darimari21/TSC/Images/1e9ec7b3-207f-4322-8b75-6b7e8333d899.PNG

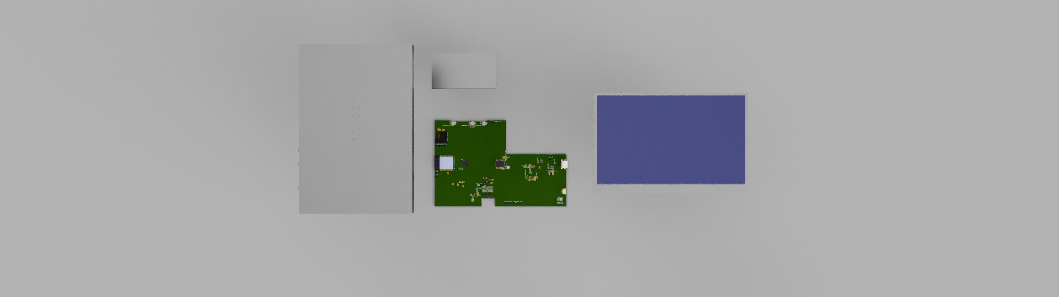
Images/1e9ec7b3-207f-4322-8b75-6b7e8333d899.PNG
