darimari21/TSC/Images/49df851a-5cd4-4d1c-8fd6-60a74a4e59ec.PNG

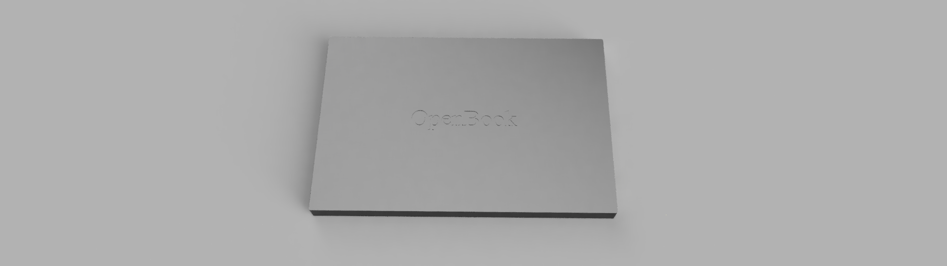
Images/49df851a-5cd4-4d1c-8fd6-60a74a4e59ec.PNG
