darimari21/TSC/Images/Screenshot 2025-04-14 140824.png

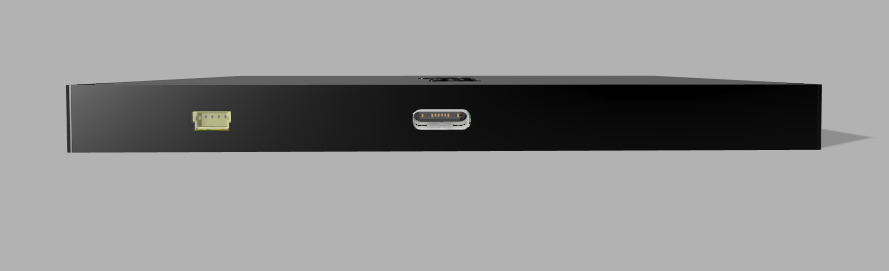
Images/Screenshot 2025-04-14 140824.png
