darimari21/TSC/Images/Screenshot 2025-04-14 141009.png

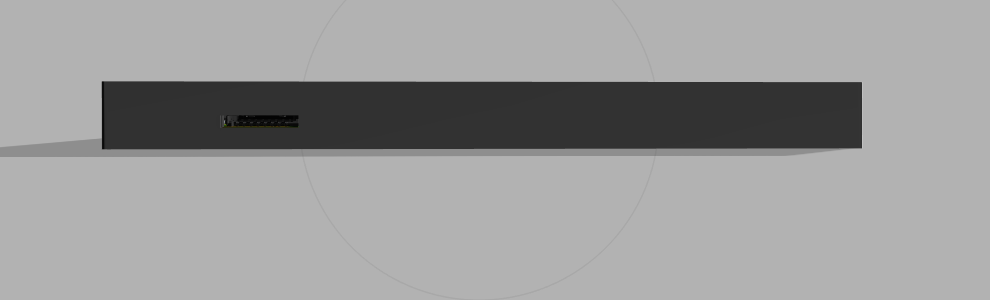
Images/Screenshot 2025-04-14 141009.png
