darimari21/TSC/Images/Screenshot 2025-04-14 141456.png

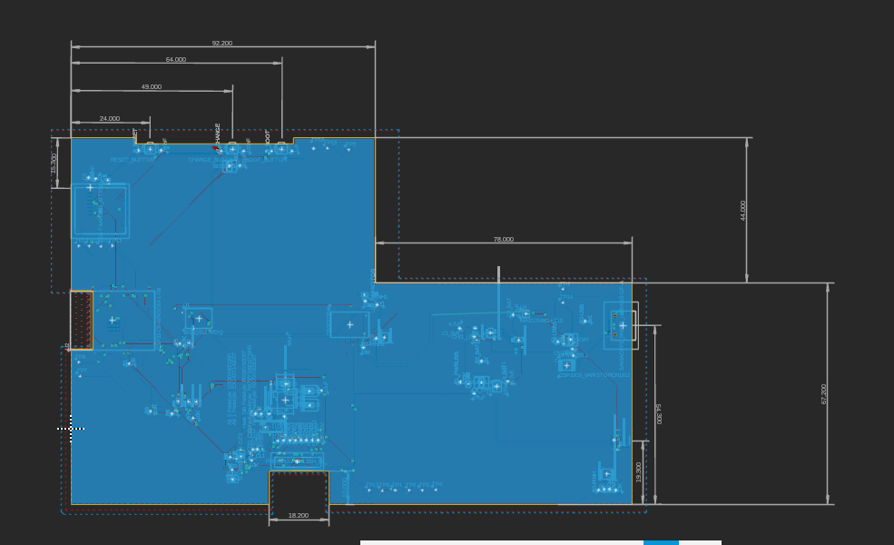
Images/Screenshot 2025-04-14 141456.png
