darimari21/TSC/Hardware/Schematic_v51.sch

## EAGLE design Hardware/Schematic_v51.sch (2025-04-06, last stored version)

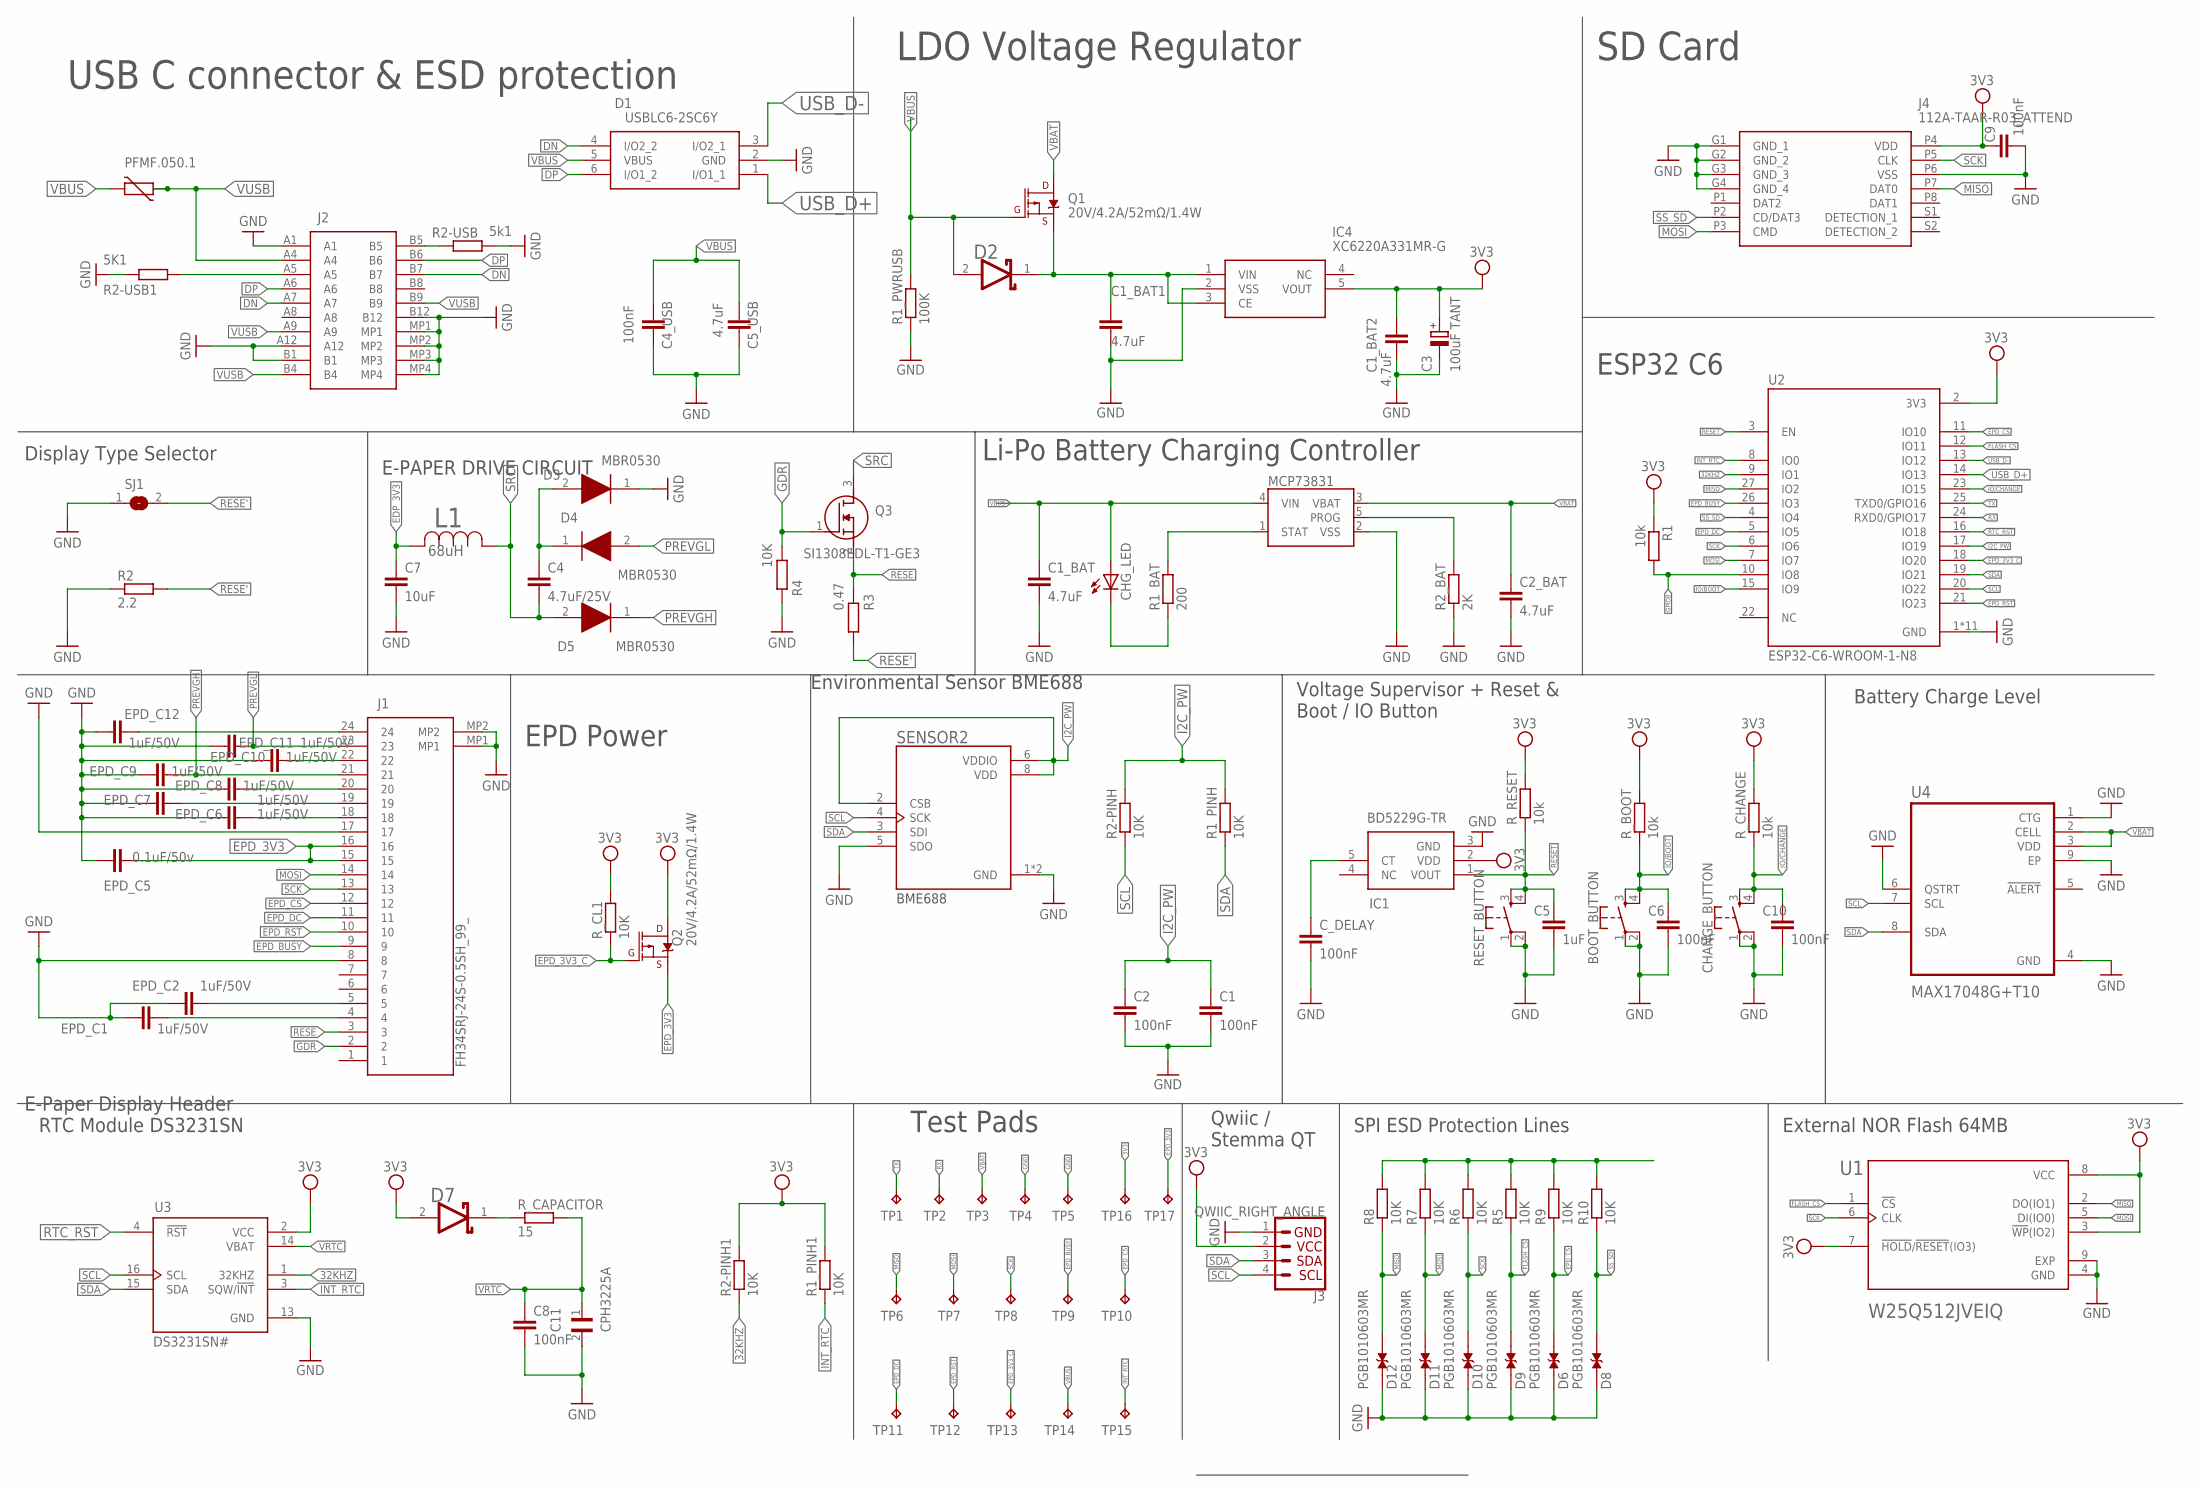
[picture p13: schematic Schematic_v51.sch]

Parts:
BOOT_BUTTON: BUTTON_CUSYOMV1; MYBUTTON
C1, C2, C4_USB, C6, C8, C9, C10: 100nF; EAGLE-LTSPICE_C0402
C1_BAT, C2_BAT, C5_USB: 4.7uF; EAGLE-LTSPICE_C0402
C1_BAT1, C1_BAT2: 4.7uF; ESP32_WROVER_EAGLE-LTSPICE_C0402
C3: 100uF TANT; RCL_CT3528
C4: 4.7uF/25V; EAGLE-LTSPICE_C0402
C5: 1uF; EAGLE-LTSPICE_C0402
C7: 10uF; EAGLE-LTSPICE_C0402
C11: CPH3225A; CAPCP3225X100N
CHANGE_BUTTON: BUTTON_CUSYOMV1; MYBUTTON
CHG_LED: ADAFRUIT_LEDCHIP-LED0603; ADAFRUIT_CHIP-LED0603
C_DELAY: 100nF; EAGLE-LTSPICE_C0402
D1: USBLC6-2SC6Y; SOT95P280X145-6N
D2, D7: ESP32_WROVER_AVX---SD0805S020S1R0_AVX_SD0805S020S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; ESP32_WROVER_AVX---SD0805S020S1R0_AVX_SD0805S020S1R0_0
D3, D4, D5: MBR0530; SOD3716X135N
D6, D8, D9, D10, D11, D12: PGB1010603MR; DIOC1608X36N
EPD_C1, EPD_C2, EPD_C6, EPD_C7, EPD_C8, EPD_C9, EPD_C10, EPD_C11, EPD_C12: 1uF/50V; EAGLE-LTSPICE_C0402
EPD_C5: 0.1uF/50v; EAGLE-LTSPICE_C0402
IC1: BD5229G-TR; SOT95P280X125-5N
IC4: XC6220A331MR-G; SOT95P280X120-5N
J1: FH34SRJ-24S-0.5SH_99_; FH34SRJ24S05SH99
J2: SAMACSYS_PARTS_USB4110-GF-A; SAMACSYS_PARTS_USB4110GFA
J3: QWIIC_RIGHT_ANGLE; JST04_1MM_RA
J4: 112A-TAAR-R03_ATTEND; 112ATAARR03ATTEND
L1: 68uH; IND_4828-WE-TPC_WRE
MCP73831: ESP32_WROVER_SPARKFUN-IC-POWER_MCP73831; ESP32_WROVER_SPARKFUN-IC-POWER_SOT23-5
PFMF.050.1: ESP32C6_VARISTORCN1812; ESP32C6_VARISTOR_CT/CN1812
Q1, Q2: 20V/4.2A/52mΩ/1.4W; ESP32_WROVER_SPARKFUN-DISCRETESEMI_SOT23-3
Q3: SI1308EDL-T1-GE3; SOT65P210X110-3N
R1: 10k; ESP32_WROVER_EAGLE-LTSPICE_R0402
R1_BAT: 200; ESP32_WROVER_EAGLE-LTSPICE_R0402
R1_PINH, R1_PINH1, R2-PINH, R2-PINH1, R4, R5, R6, R7, R8, R9, R10: 10K; ESP32_WROVER_EAGLE-LTSPICE_R0402
R1_PWRUSB: 100K; ESP32_WROVER_EAGLE-LTSPICE_R0402
R2: 2.2; ESP32_WROVER_EAGLE-LTSPICE_R0402
R2-USB: 5k1; ESP32_WROVER_EAGLE-LTSPICE_R0402
R2-USB1: 5K1; ESP32_WROVER_EAGLE-LTSPICE_R0402
R2_BAT: 2K; ESP32_WROVER_EAGLE-LTSPICE_R0402
R3: 0.47; ESP32_WROVER_EAGLE-LTSPICE_R0402
RESET_BUTTON: BUTTON_CUSYOMV1; MYBUTTON
R_BOOT: 10k; ESP32_WROVER_EAGLE-LTSPICE_R0402
R_CAPACITOR: 15; ESP32_WROVER_EAGLE-LTSPICE_R0402
R_CHANGE: 10k; ESP32_WROVER_EAGLE-LTSPICE_R0402
R_CL1: 10K; ESP32_WROVER_EAGLE-LTSPICE_R0402
R_RESET: 10k; ESP32_WROVER_EAGLE-LTSPICE_R0402
SENSOR2: ESP32_WROVER_BME680_BME680; ESP32_WROVER_BME680_PSON80P300X300X100-8N
SJ1: SJ
TP1, TP2, TP3, TP4, TP5, TP6, TP7, TP8, TP9, TP10, TP11, TP12, TP13, TP14, TP15, TP16, TP17: TPTP20R; TP20R
U1: W25Q512JVEIQ; SON127P600X800X80-9N
U2: ESP32-C6-WROOM-1-N8; XCVR_ESP32-C6-WROOM-1-N8
U3: DS3231SN#; SOIC127P1032X265-16N
U4: MAX17048G+T10; SON50P200X200X80-9N

Connections:
3V3: C1_BAT2.1, C3.+, C9.2, D7.2 (ANODE), IC1.2 (VDD), IC4.5 (VOUT), J3.2, J4.P4 (VDD), Q2.3 (D), R1.1, R1_PINH1.2, R2-PINH1.2, R_BOOT.2, R_CHANGE.2, R_CL1.2, R_RESET.2, TP16.TP, U1.3 (!WP!(IO2)), U1.7 (!HOLD!/!RESET!(IO3)), U1.8 (VCC), U2.2 (3V3), U3.2 (VCC)
32KHZ: R2-PINH1.1, U2.9 (IO1), U3.1 (32KHZ)
DN: D1.4 (I/O2_2), J2.A7, J2.B7
DP: D1.6 (I/O1_2), J2.A6, J2.B6
EDP_3V3: C7.1, L1.2
EPD_3V3: EPD_C5.2, J1.15, J1.16, Q2.2 (S), TP17.TP
EPD_3V3_C: Q2.1 (G), R_CL1.1, TP13.TP, U2.18 (IO20)
EPD_BUSY: J1.9, TP9.TP, U2.26 (IO3)
EPD_CS: D6.2, J1.12, R9.1, TP10.TP, U2.11 (IO10)
EPD_DC: J1.11, TP11.TP, U2.5 (IO5)
EPD_RST: J1.10, TP12.TP, U2.21 (IO23)
FLASH_CS: D9.2, R5.1, U1.1 (!CS), U2.12 (IO11)
GDR: J1.2, Q3.1 (G), R4.2
GND: BOOT_BUTTON.1, BOOT_BUTTON.2, C1.2, C1_BAT.2, C1_BAT1.2, C1_BAT2.2, C2.2, C2_BAT.2, C3.-, C4_USB.2, C5.2, C5_USB.2, C6.2, C7.2, C8.2, C9.1, C10.2, C11.2, CHANGE_BUTTON.1, CHANGE_BUTTON.2, C_DELAY.2, D1.2 (GND), D3.1 (K), D6.1, D8.1, D9.1, D10.1, D11.1, D12.1, EPD_C1.1, EPD_C2.1, EPD_C5.1, EPD_C6.1, EPD_C7.1, EPD_C8.1, EPD_C9.1, EPD_C10.1, EPD_C11.1, EPD_C12.1, IC1.3 (GND), IC4.2 (VSS), J1.8, J1.17, J1.MP1, J1.MP2, J2.A1, J2.A12, J2.B1, J2.B12, J2.MP1, J2.MP2, J2.MP3, J2.MP4, J3.1, J4.G1 (GND_1), J4.G2 (GND_2), J4.G3 (GND_3), J4.G4 (GND_4), J4.P6 (VSS), MCP73831.2 (VSS), R1_PWRUSB.1, R2.1, R2-USB.2, R2-USB1.1, R2_BAT.1, R4.1, RESET_BUTTON.1, RESET_BUTTON.2, SENSOR2.1 (GND), SENSOR2.5 (SDO), SJ1.1, TP4.TP, TP5.TP, U1.4 (GND), U1.9 (EXP), U2.1 (GND), U3.13 (GND), U4.1 (CTG), U4.4 (GND), U4.6 (QSTRT), U4.9 (EP)
GPIO8: R1.2, U2.10 (IO8)
I2C_PW: C1.1, C2.1, R1_PINH.2, R2-PINH.2, SENSOR2.2 (CSB), SENSOR2.6 (VDDIO), SENSOR2.8 (VDD), U2.17 (IO19)
INT_RTC: R1_PINH1.1, TP15.TP, U2.8 (IO0), U3.3 (SQW/!INT)
IO/BOOT: BOOT_BUTTON.3, BOOT_BUTTON.4, C6.1, R_BOOT.1, U2.15 (IO9)
IO/CHANGE: C10.1, CHANGE_BUTTON.3, CHANGE_BUTTON.4, R_CHANGE.1, U2.23 (IO15)
MISO: D12.2, J4.P7 (DAT0), R8.1, TP6.TP, U1.2 (DO(IO1)), U2.27 (IO2)
MOSI: D11.2, J1.14, J4.P3 (CMD), R7.1, TP7.TP, U1.5 (DI(IO0)), U2.7 (IO7)
unnamed: C4.1, D3.2 (A), D4.1 (K)
unnamed: EPD_C12.2, J1.24
unnamed: J2.A5, R2-USB1.2
unnamed: J2.B5, R2-USB.1
unnamed: R5.2, R6.2, R7.2, R8.2, R9.2, R10.2
unnamed: C1_BAT1.1, D2.1 (CATHODE), IC4.1 (VIN), IC4.3 (CE), Q1.2 (S)
unnamed: D7.1 (CATHODE), R_CAPACITOR.1
unnamed: EPD_C10.2, J1.22
unnamed: EPD_C8.2, J1.20
unnamed: EPD_C7.2, J1.19
unnamed: EPD_C6.2, J1.18
unnamed: EPD_C2.2, J1.5
unnamed: C_DELAY.1, IC1.5 (CT)
unnamed: EPD_C1.2, J1.4
unnamed: MCP73831.5 (PROG), R2_BAT.2
unnamed: CHG_LED.C, R1_BAT.1
unnamed: MCP73831.1 (STAT), R1_BAT.2
PREVGH: D5.1 (K), EPD_C9.2, J1.21
PREVGL: D4.2 (A), EPD_C11.2, J1.23
RESE: J1.3, Q3.2 (S), R3.2
RESE': R2.2, R3.1, SJ1.2
RESET: C5.1, IC1.1 (VOUT), RESET_BUTTON.3, RESET_BUTTON.4, R_RESET.1, U2.3 (EN)
RTC_RST: U2.16 (IO18), U3.4 (!RST)
RX: TP2.TP, U2.24 (RXD0/GPIO17)
SCK: D10.2, J1.13, J4.P5 (CLK), R6.1, TP8.TP, U1.6 (CLK), U2.6 (IO6)
SCL: J3.4, R2-PINH.1, SENSOR2.4 (SCK), U2.20 (IO22), U3.16 (SCL), U4.7 (SCL)
SDA: J3.3, R1_PINH.1, SENSOR2.3 (SDI), U2.19 (IO21), U3.15 (SDA), U4.8 (SDA)
SRC: C4.2, D5.2 (A), L1.1, Q3.3 (D)
SS_SD: D8.2, J4.P2 (CD/DAT3), R10.1, U2.4 (IO4)
TX: TP1.TP, U2.25 (TXD0/GPIO16)
USB_D+: D1.1 (I/O1_1), U2.14 (IO13)
USB_D-: D1.3 (I/O2_1), U2.13 (IO12)
VBAT: C2_BAT.1, MCP73831.3 (VBAT), Q1.3 (D), TP3.TP, U4.2 (CELL), U4.3 (VDD)
VBUS: C1_BAT.1, C4_USB.1, C5_USB.1, CHG_LED.A, D1.5 (VBUS), D2.2 (ANODE), MCP73831.4 (VIN), PFMF.050.1.2, Q1.1 (G), R1_PWRUSB.2, TP14.TP
VRTC: C8.1, C11.1, R_CAPACITOR.2, U3.14 (VBAT)
VUSB: J2.A4, J2.A9, J2.B4, J2.B9, PFMF.050.1.1

Notes on the sheet:
USB C connector & ESD protection
LDO Voltage Regulator
SD Card
Display Type Selector
E-PAPER DRIVE CIRCUIT
E-Paper Display Header
EPD Power
BME688
Environmental Sensor BME688
Test Pads
ESP32 C6
Li-Po Battery Charging Controller
Voltage Supervisor + Reset & Boot / IO Button
Battery Charge Level
SPI ESD Protection Lines
External NOR Flash 64MB
Qwiic / Stemma QT
RTC Module DS3231SN
